ManchesterStingerMotorsports/gear-shifter/production_firmware/main/interrupts/shift_inputs.hpp

#pragma once

#include "esp_err.h"
#include "freertos/FreeRTOS.h"
#include "freertos/task.h"

// Shift request values latched by the GPIO ISRs.
enum ShiftRequest
{
    SHIFT_REQUEST_NONE = 0,
    SHIFT_REQUEST_UP,
    SHIFT_REQUEST_DOWN,
};

// Configure the shift input GPIOs and register their ISRs.
esp_err_t setup_shift_inputs(TaskHandle_t shift_task_handle);

// Take the pending request and clear the shared latch.
ShiftRequest consume_pending_shift_request();

// Clear stale input state and re-enable the shift GPIO interrupts.
void clear_and_enable_shift_inputs();

void shift_up_isr(void *arg);
void shift_down_isr(void *arg);
